SP5GW/Regenerative_Radio_Receiver/img/LC_outA_DetOut_D_meas_D.png

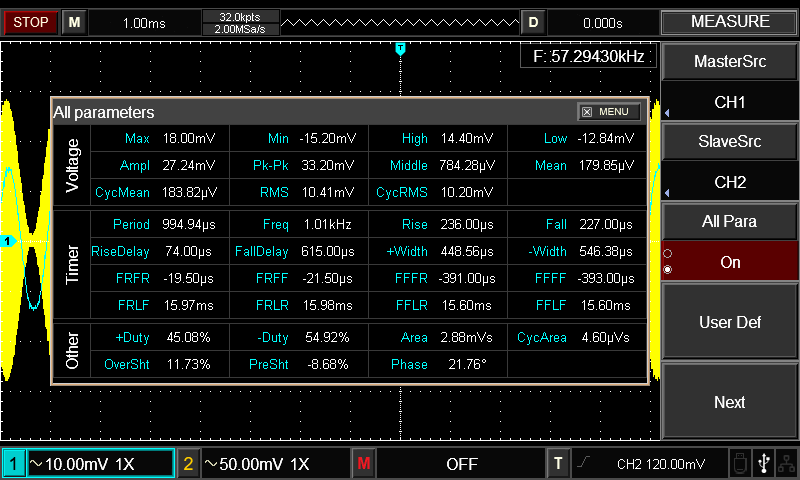
img/LC_outA_DetOut_D_meas_D.png
