SP5GW/Regenerative_Radio_Receiver/docs/Detector_Radio_ver2.kicad_sch

## KiCad design docs/Detector_Radio_ver2.kicad_sch (2025-02-13)

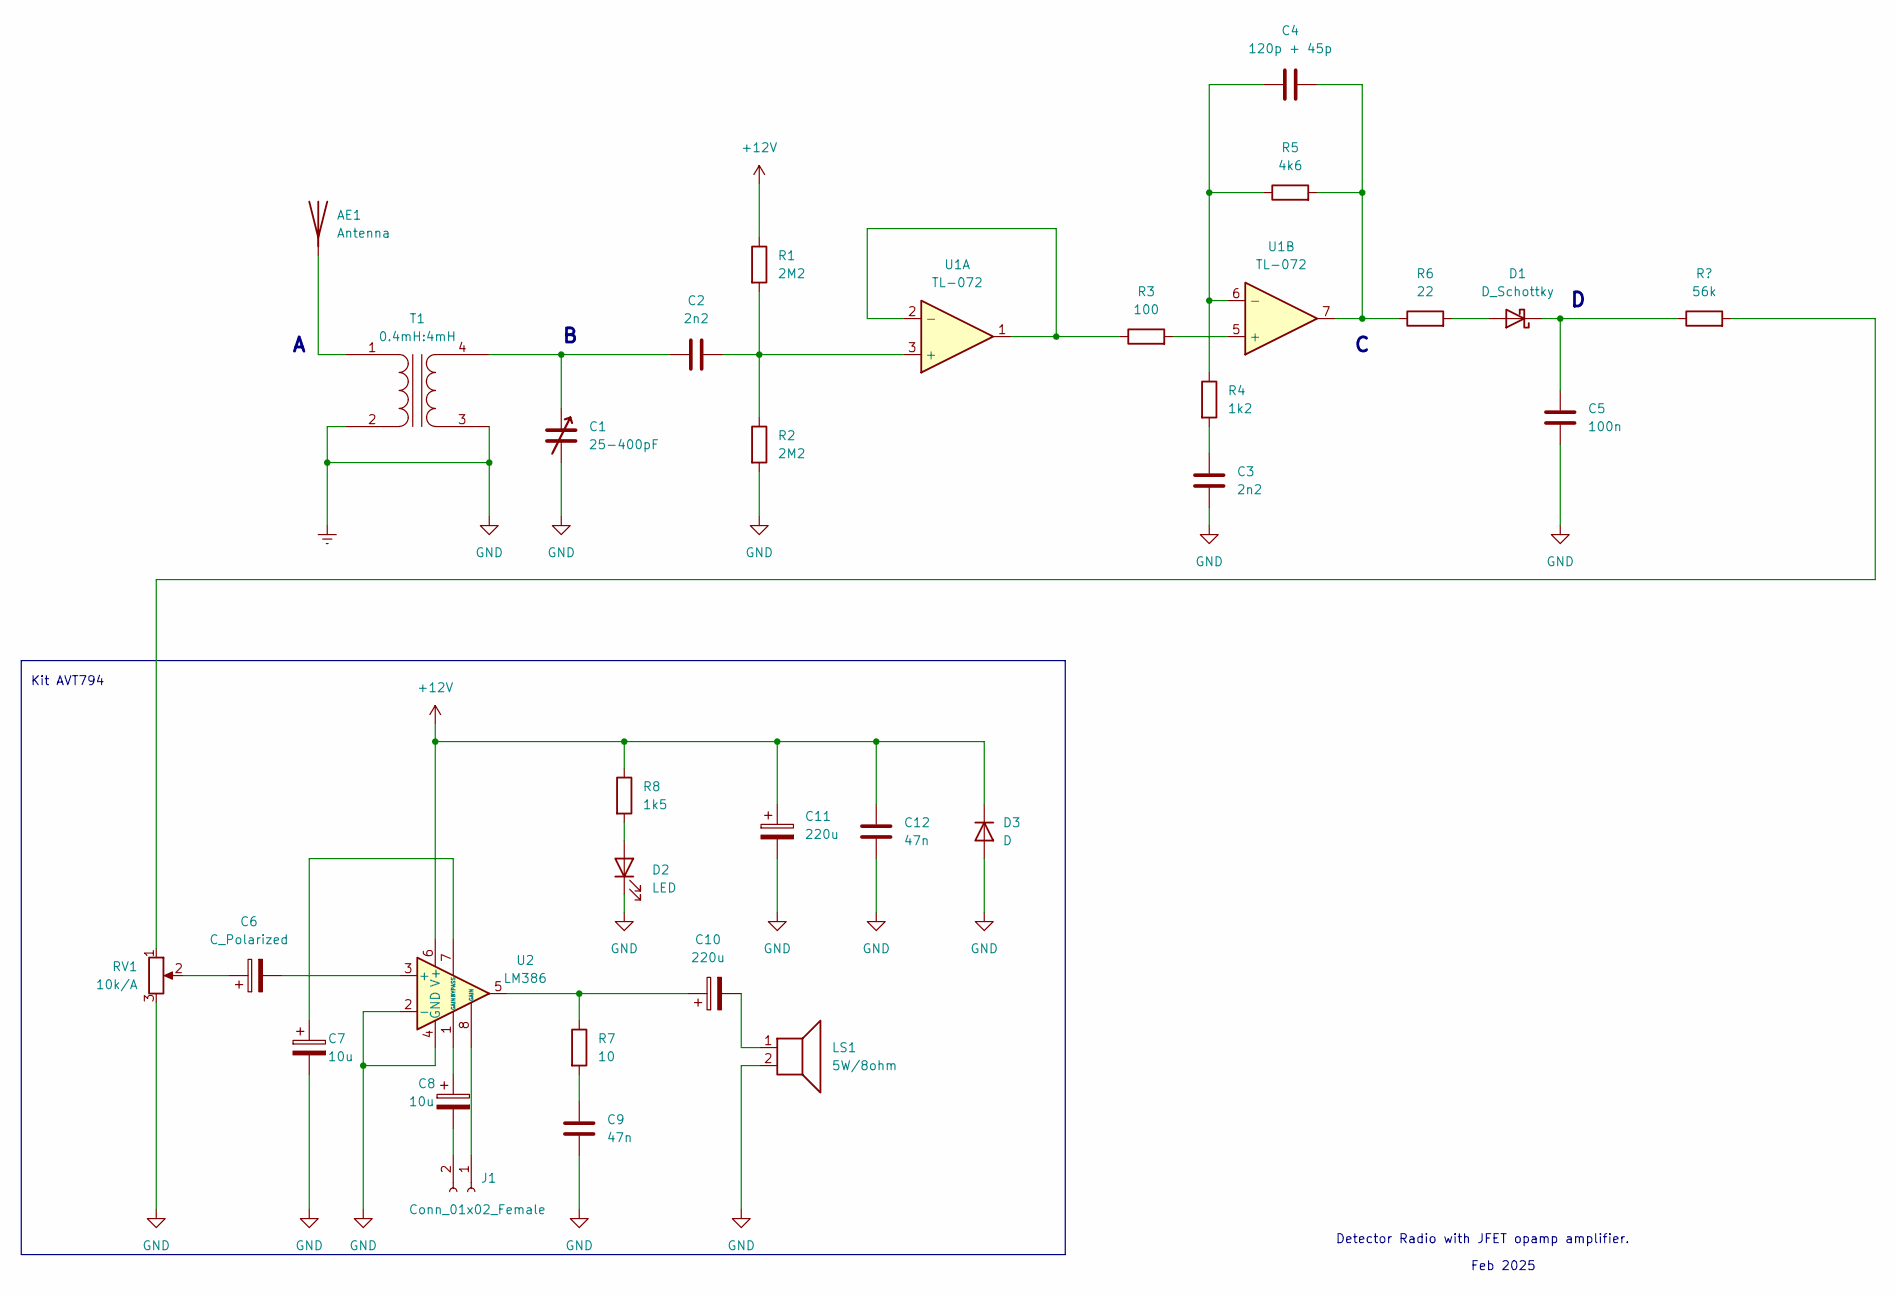
[picture p12: schematic Detector_Radio_ver2.kicad_sch]

Parts:
AE1: Antenna
C1: 25-400pF
C2, C3: 2n2
C4: 120p + 45p
C5: 100n
C6: C_Polarized
C7, C8: 10u
C9, C12: 47n
C10, C11: 220u
D1: D_Schottky
D2: LED
D3: D
J1: Conn_01x02_Female
LS1: 5W/8ohm
R1, R2: 2M2
R3: 100
R4: 1k2
R5: 4k6
R6: 22
R7: 10
R8: 1k5
RV1: 10k/A
T1: 0.4mH:4mH
U1: TL-072
U2: LM386

Connections:
+12V: C11.1, C12.1, D3.1 (K), R1.1, R8.1, U2.6 (V+)
Earth: C1.2, C3.2, C5.2, C7.2, C9.2, C11.2, C12.2, D2.1 (K), D3.2 (A), LS1.2, R2.2, RV1.3, T1.2 (AB), T1.3 (SA), U2.2 (-), U2.4 (GND)
unnamed: AE1.1, T1.1 (AA)
unnamed: C1.1, C2.1, T1.4 (SB)
unnamed: C2.2, R1.2, R2.1, U1.3 (+)
unnamed: C3.1, R4.2
unnamed: C4.1, R4.1, R5.1, U1.6 (-)
unnamed: C4.2, R5.2, R6.1, U1.7
unnamed: C5.1, D1.1 (K)
unnamed: C6.1, RV1.2
unnamed: C6.2, U2.3 (+)
unnamed: C7.1, U2.7 (BYPASS)
unnamed: C8.1, U2.1 (GAIN)
unnamed: C8.2, J1.2
unnamed: C9.1, R7.2
unnamed: C10.1, R7.1, U2.5
unnamed: C10.2, LS1.1
unnamed: D1.2 (A), R6.2
unnamed: D2.2 (A), R8.2
unnamed: J1.1, U2.8 (GAIN)
unnamed: R3.1, U1.1, U1.2 (-)
unnamed: R3.2, U1.5 (+)

Notes on the sheet:
Feb 2025
Detector Radio with JFET opamp amplifier.
Kit AVT794
